Maddimax/MadControl/Software/IOTest/InputChannels.h

#pragma once


template<int kNumChannels>
class InputChannels
{
  InputChannel* _channel[kNumChannels];
  
  ExpoFilter _globalExpo;
  LinearFilter _globalLinear;
  
public:
  InputChannels()
  {
    for(int i=0;i<kNumChannels;i++)
    {
      _channel[i] = new InputChannel();
    }
  }
  
  ExpoFilter* globalExpo()
  {
    return &_globalExpo; 
  }
  
  LinearFilter* globalLinear()
  {
    return &_globalLinear;
  }
  
  float mapValueForChannel(float v, byte id) const
  {
    float result = v;
    result = _globalExpo.map(result, _channel[id]->isBipolar());
    result = _channel[id]->map(result);
    result = _globalLinear.map(result, _channel[id]->isBipolar());
    return result;
  }
  
  float channelValue(byte id) const
  {
    float result = _channel[id]->adcValue();
    result = _globalExpo.map(result, _channel[id]->isBipolar());
    result = _channel[id]->map(result);
    result = _globalLinear.map(result, _channel[id]->isBipolar());

    return result;
  }
  
  InputChannel* channel(byte id) const
  {
    return _channel[id]; 
  }
  
  void updateFromAdc(const TADCChannels& adcChannels)
  {
    for(int i=0;i<kNumChannels;i++)
    {
      _channel[i]->setADCValue(adcChannels.channel(i)->value());  
    }
  }
};

typedef InputChannels<NUM_INCHANNELS> TInputChannels;
